berg-lab/Steam-Trap-Mic/firmware/changelog.h

//=========================================================================================================
// changelog.h - Defines the update history for this source code
//=========================================================================================================
#ifndef _CHANGELOG_H_
#define _CHANGELOG_H_

//=========================================================================================================
// Vers   When      Who      What
//---------------------------------------------------------------------------------------------------------
// 1000  09-Sep-22  JRM      Initial creation
//                           
//=========================================================================================================
#define FW_VERSION 1005

#endif
